simonroedig/PrivacyDeck/privacyDeck/os/blackout_images/img1.jpg

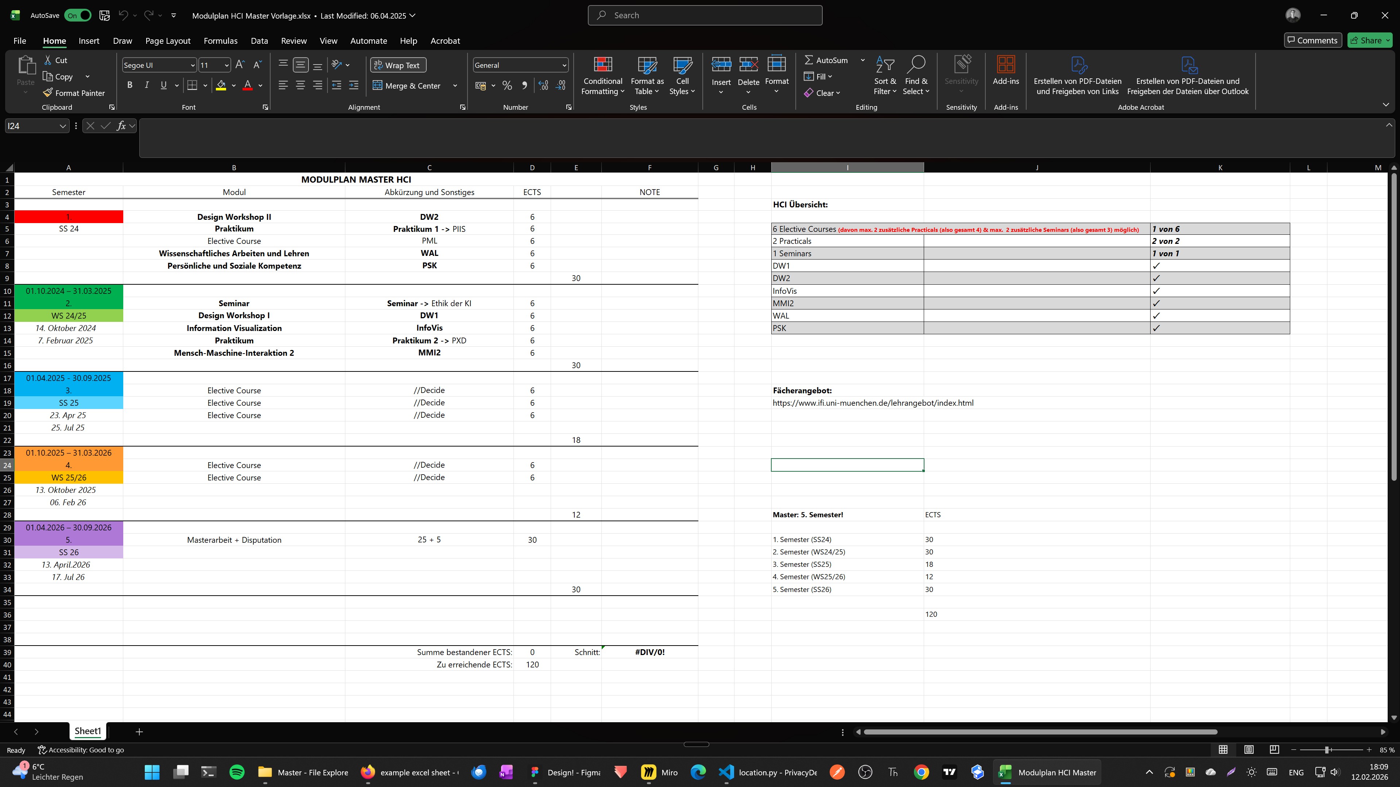
privacyDeck/os/blackout_images/img1.jpg
