simonroedig/PrivacyDeck/privacyDeck/os/blackout_images/img2.jpg

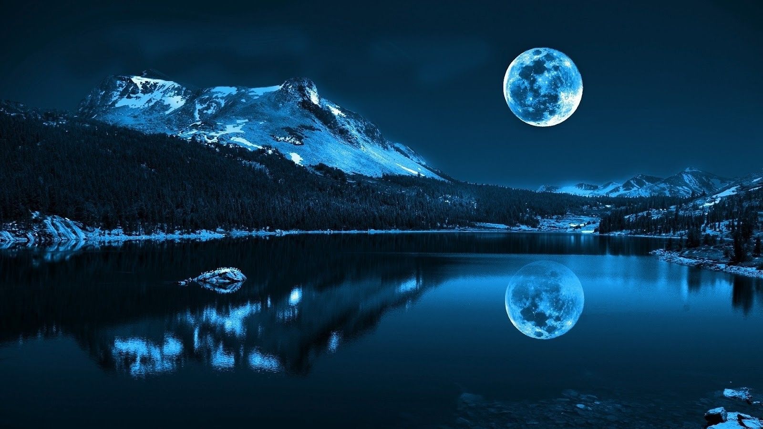
privacyDeck/os/blackout_images/img2.jpg
